0x007E/wfg/WFG.asc

C1: cap; 100n
C2: cap; 1µ
R1: EuropeanResistor; 4k7
R2: EuropeanResistor; 5k
R3: EuropeanResistor; 5k
R4: EuropeanResistor; 1k
R5: EuropeanResistor; 2k
R6: EuropeanResistor; 5k
R7: EuropeanResistor; 5k
R8: EuropeanResistor; 1k
R9: EuropeanResistor; 1Meg
U1: OP07
U2: OP07
U3: OP07
U4: OP07
V1: voltage; 5
Named nets: VCC, 0, V_TRI, V_PWM
.tran 0 1s 2m 2.25m startup
